Mic-Tsai/HECS_Electronic-Pixel_X/Pixel-X_Image/Original/de-lux-2.jpg

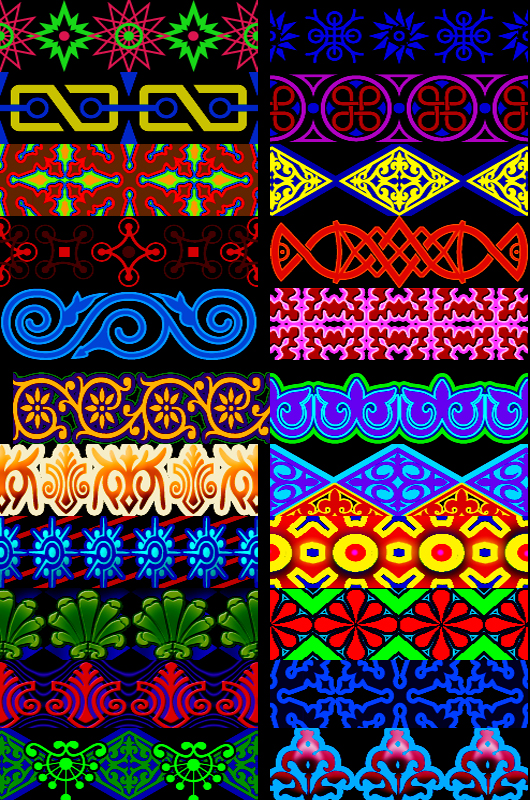
Pixel-X_Image/Original/de-lux-2.jpg
