Mic-Tsai/HECS_Electronic-Pixel_X/Pixel-X_Image/Original/e17fa6a1781008a12646bba379d51568.jpg

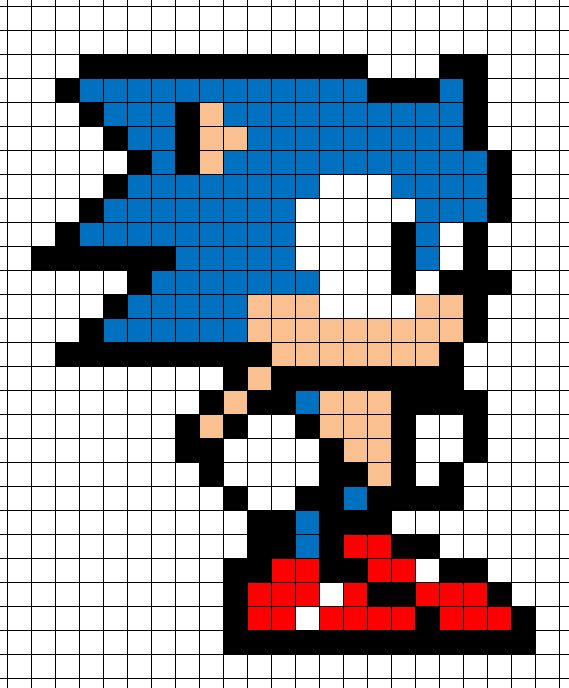
Pixel-X_Image/Original/e17fa6a1781008a12646bba379d51568.jpg
