Mic-Tsai/HECS_Electronic-Pixel_X/Pixel-X_Image/Original/taiwan-map.png

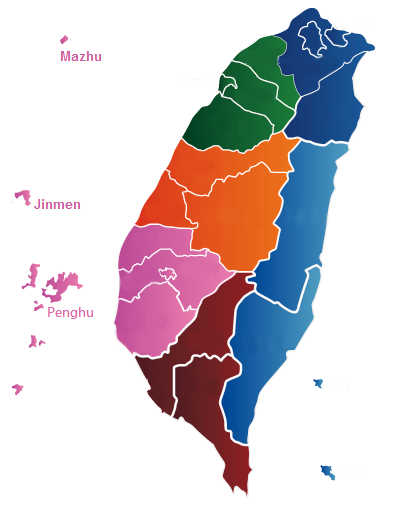
Pixel-X_Image/Original/taiwan-map.png
