Mic-Tsai/HECS_Electronic-Pixel_X/Pixel-X_Image/Original/tumblr_inline_nwlr92iqKI1tyob45_540.png

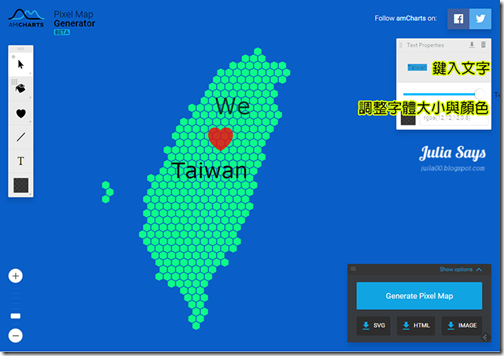
Pixel-X_Image/Original/tumblr_inline_nwlr92iqKI1tyob45_540.png
